mauroalderete/3dprinter/Zero/Design Model 0/CuplaFlexible58.SLDPRT

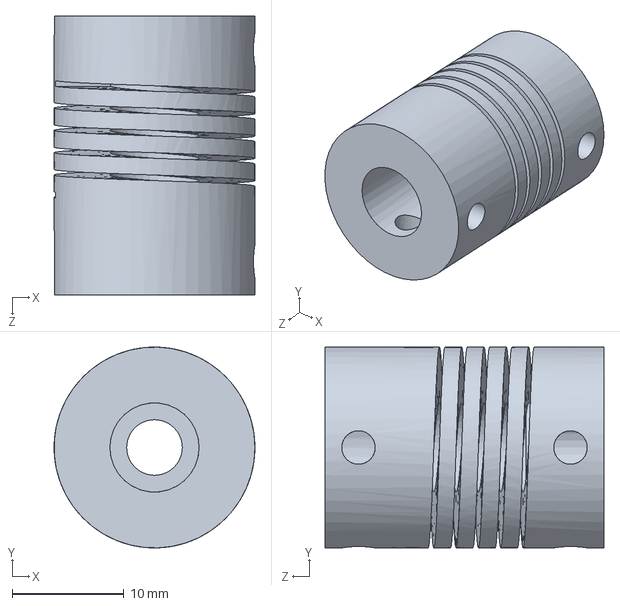
[picture p16: CAD file, 2018-10-06]
Zero/Design Model 0/CuplaFlexible58.SLDPRT
18.0 x 18.0 x 25.0 mm
