mauroalderete/3dprinter/Zero/Design Model 0/Manufacture/LateralRight.SLDPRT

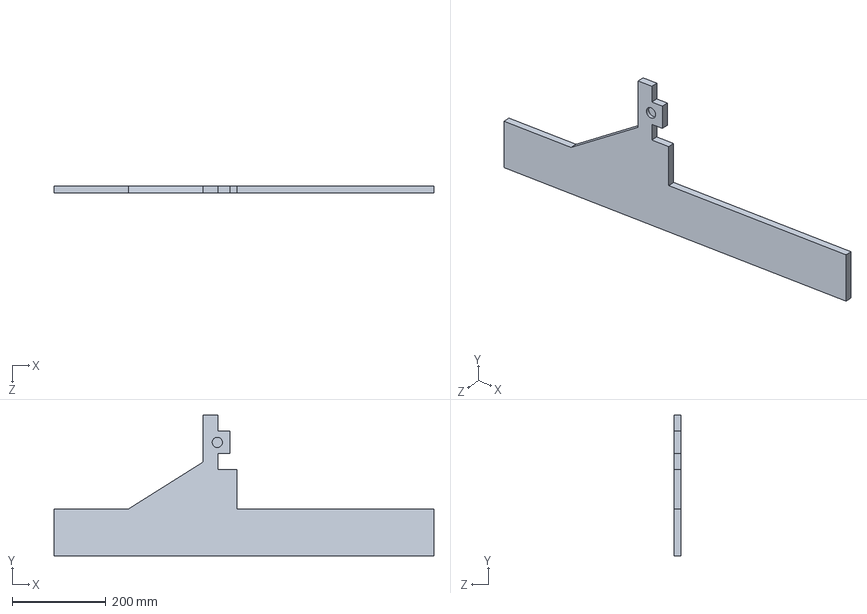
[picture p17: CAD file, 2018-10-08]
Zero/Design Model 0/Manufacture/LateralRight.SLDPRT
811.2 x 300.0 x 15.0 mm
