mauroalderete/3dprinter/Zero/Design Model 1/FuentePC.SLDPRT

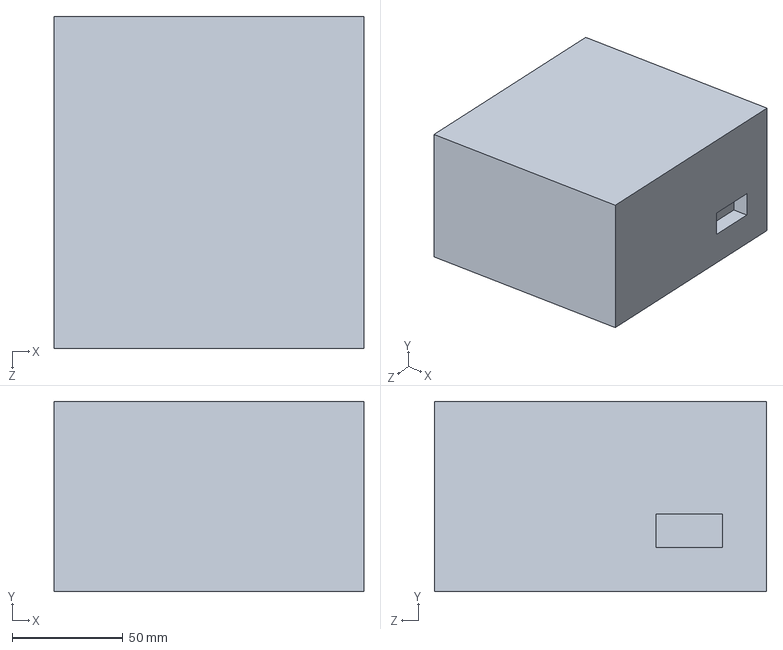
[picture p18: CAD file, 2018-10-14]
Zero/Design Model 1/FuentePC.SLDPRT
140.0 x 86.0 x 150.0 mm
