mauroalderete/3dprinter/Zero/Design Model 0/ConceptTests/EjeZ Invertido/SoporteEjeZ.SLDPRT

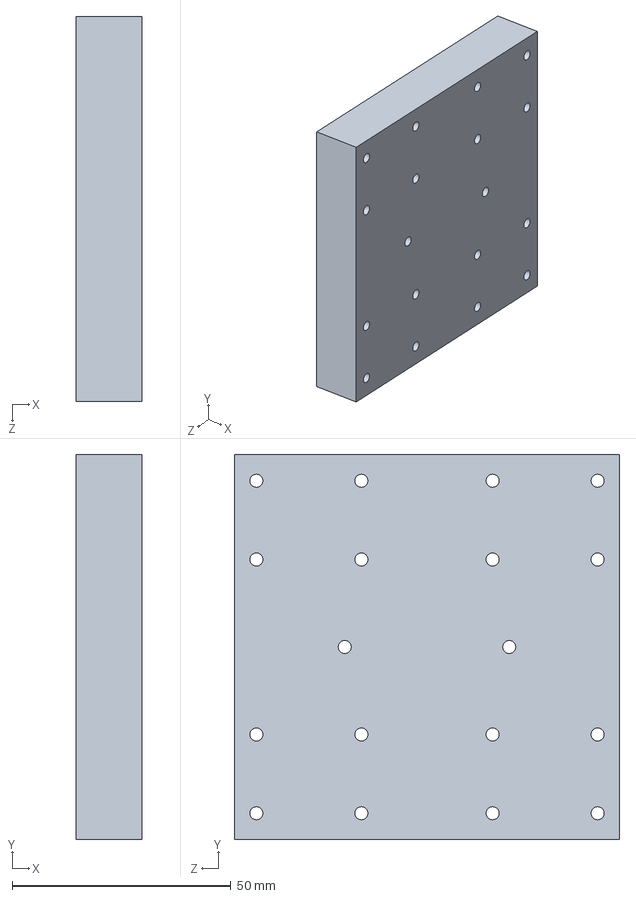
[picture p19: CAD file, 2018-10-09]
Zero/Design Model 0/ConceptTests/EjeZ Invertido/SoporteEjeZ.SLDPRT
15.0 x 88.0 x 88.0 mm
