mauroalderete/3dprinter/Zero/Design Model 0/TuercaTHSL8-Soporte.SLDPRT

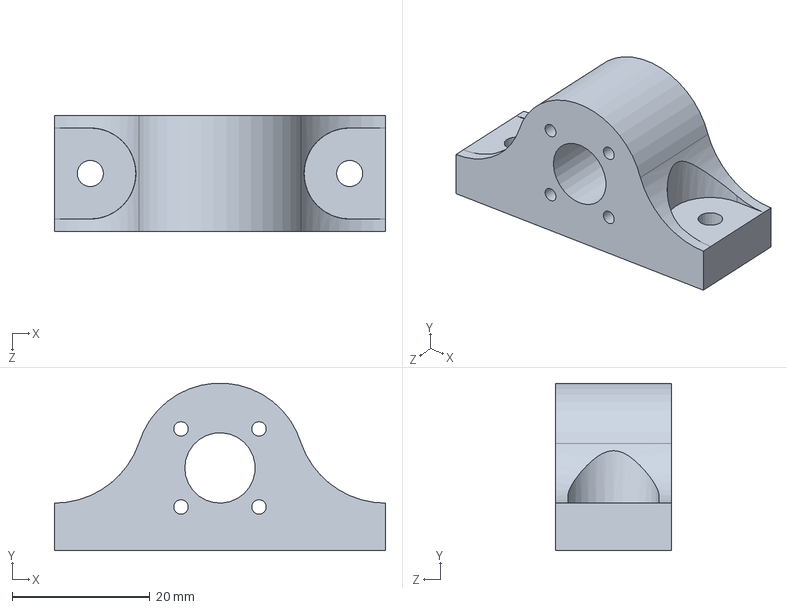
[picture p20: CAD file, 2018-10-06]
Zero/Design Model 0/TuercaTHSL8-Soporte.SLDPRT
48.0 x 24.3 x 16.8 mm
