mauroalderete/3dprinter/Zero/Design Model 1/Dremel-SoporteCabezal.SLDPRT

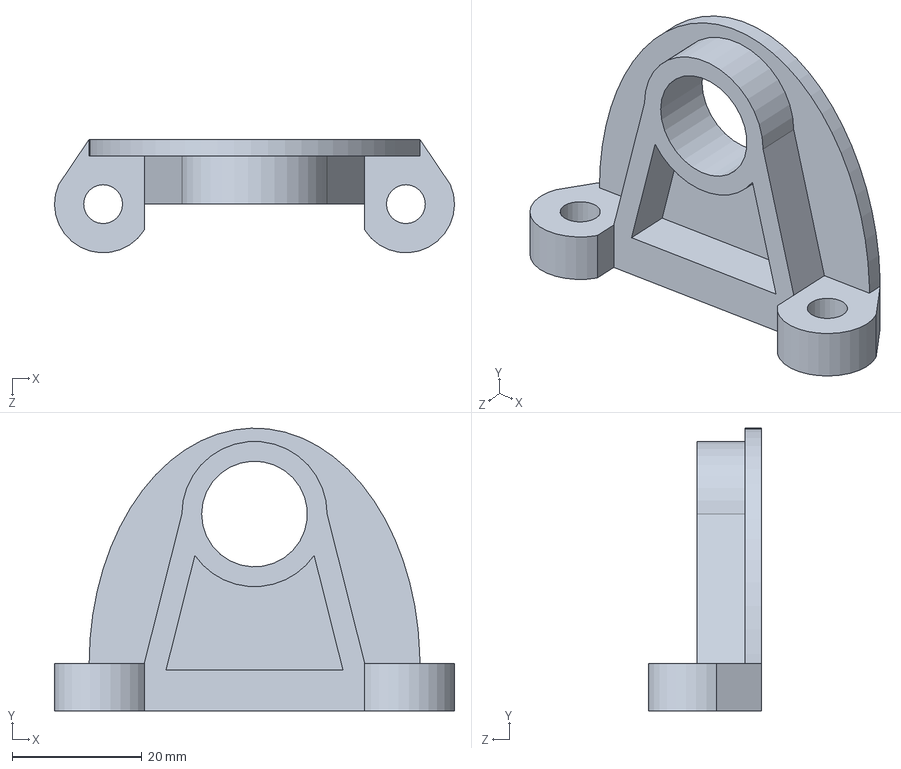
[picture p21: CAD file, 2018-10-14]
Zero/Design Model 1/Dremel-SoporteCabezal.SLDPRT
61.7 x 43.6 x 17.5 mm
