mauroalderete/3dprinter/Zero/Design Model 1/Manufacture/BaseMinitorno.SLDPRT

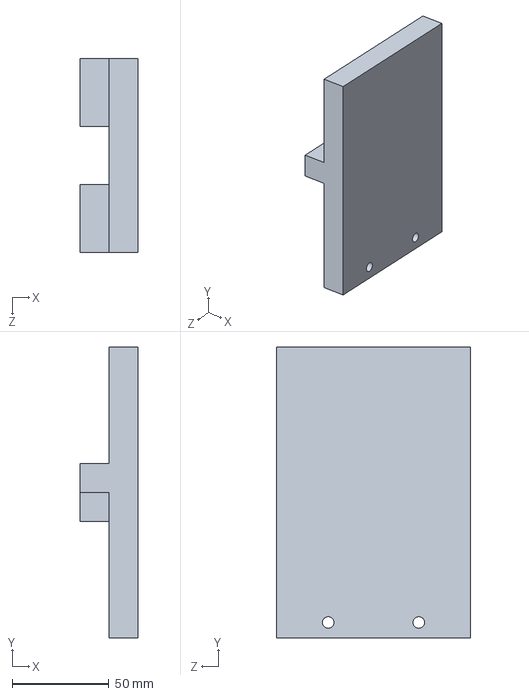
[picture p22: CAD file, 2018-10-14]
Zero/Design Model 1/Manufacture/BaseMinitorno.SLDPRT
30.0 x 150.0 x 100.0 mm
