mauroalderete/3dprinter/Zero/Design Model 0/TuercaTHSL8.SLDPRT

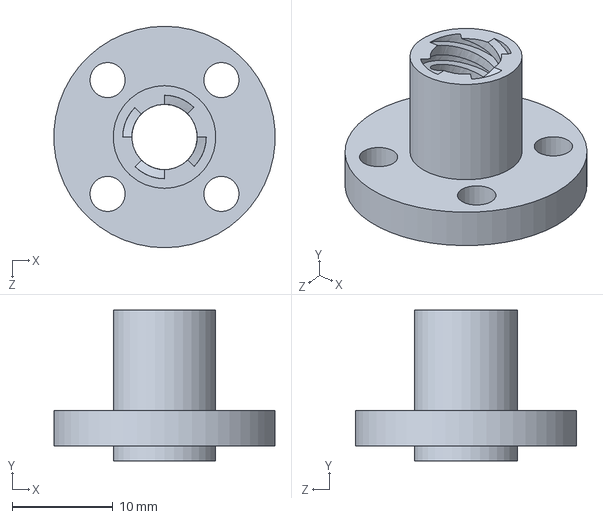
[picture p23: CAD file, 2018-10-06]
Zero/Design Model 0/TuercaTHSL8.SLDPRT
22.0 x 15.0 x 22.0 mm
