mauroalderete/3dprinter/Zero/Design Model 1/BaseElectronica.SLDPRT

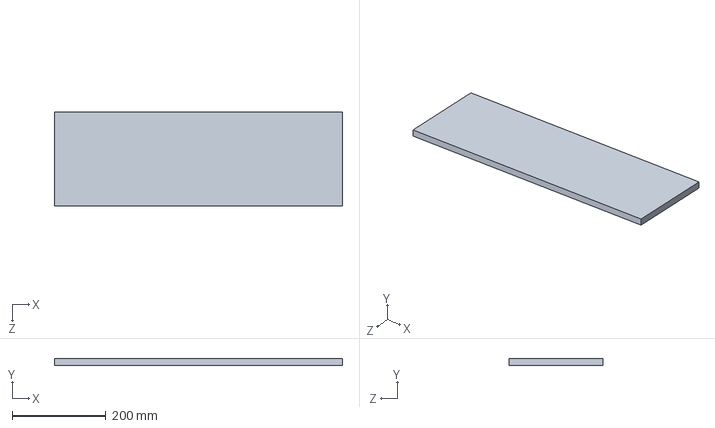
[picture p24: CAD file, 2018-10-14]
Zero/Design Model 1/BaseElectronica.SLDPRT
615.0 x 15.0 x 200.0 mm
