mauroalderete/3dprinter/Zero/Design Model 1/Manufacture/ZFloor.SLDPRT

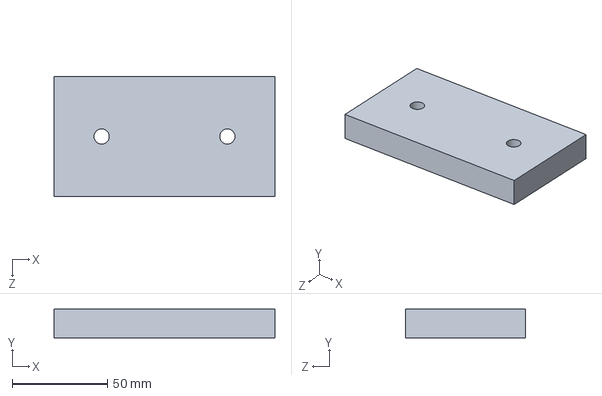
[picture p25: CAD file, 2018-10-12]
Zero/Design Model 1/Manufacture/ZFloor.SLDPRT
116.0 x 15.0 x 63.0 mm
