mauroalderete/3dprinter/Zero/Design Model 0/Manufacture/LateralArco.SLDPRT

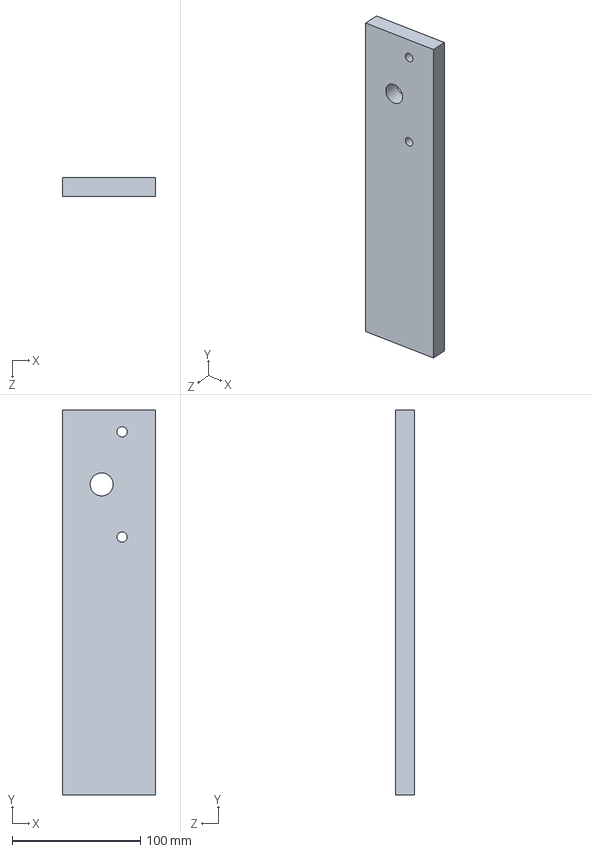
[picture p26: CAD file, 2018-10-08]
Zero/Design Model 0/Manufacture/LateralArco.SLDPRT
72.5 x 300.0 x 15.0 mm
