mauroalderete/3dprinter/Zero/Design Model 1/Manufacture/BaseTool.SLDPRT

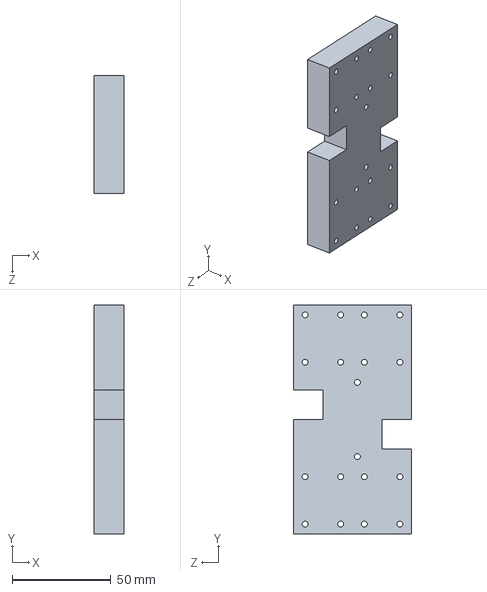
[picture p27: CAD file, 2018-10-12]
Zero/Design Model 1/Manufacture/BaseTool.SLDPRT
15.0 x 116.0 x 60.0 mm
