mauroalderete/3dprinter/Zero/Design Model 1/Minitorno.SLDPRT

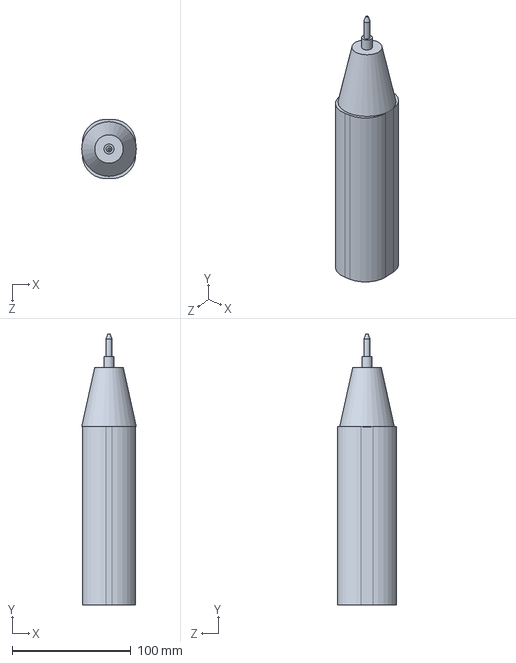
[picture p28: CAD file, 2018-10-14]
Zero/Design Model 1/Minitorno.SLDPRT
46.0 x 228.0 x 50.0 mm
