mauroalderete/3dprinter/Zero/Design Model 0/Manufacture/LateralSoporteEjeX.SLDPRT

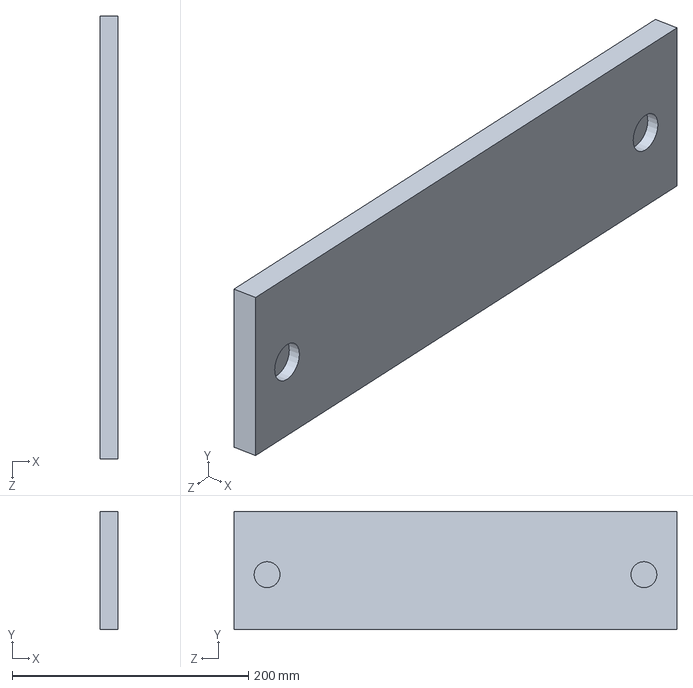
[picture p29: CAD file, 2018-10-08]
Zero/Design Model 0/Manufacture/LateralSoporteEjeX.SLDPRT
15.0 x 100.0 x 375.0 mm
