mauroalderete/3dprinter/Zero/Design Model 0/NEMA17-Soporte.SLDPRT

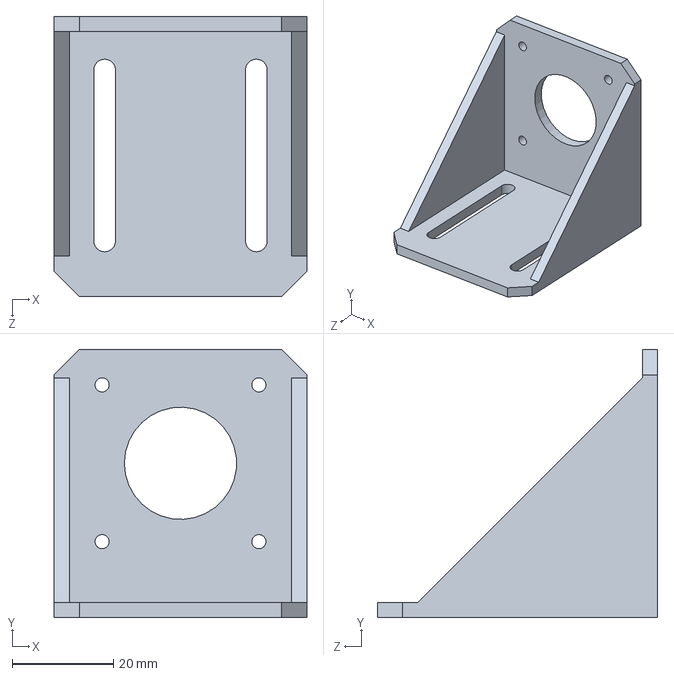
[picture p30: CAD file, 2018-10-06]
Zero/Design Model 0/NEMA17-Soporte.SLDPRT
50.0 x 53.0 x 55.4 mm
