mauroalderete/3dprinter/Zero/Design Model 1/Manufacture/BaseExtrusor.SLDPRT

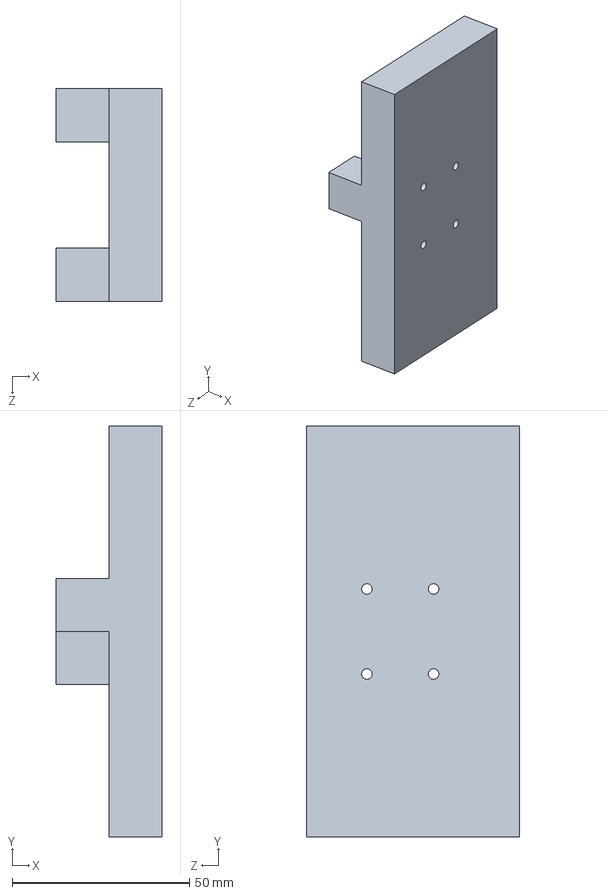
[picture p31: CAD file, 2018-10-12]
Zero/Design Model 1/Manufacture/BaseExtrusor.SLDPRT
30.0 x 116.0 x 60.0 mm
