mauroalderete/3dprinter/Zero/Design Model 1/ZPiso.SLDPRT

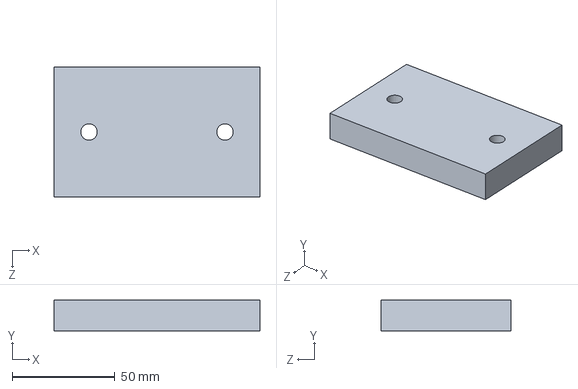
[picture p32: CAD file, 2018-10-12]
Zero/Design Model 1/ZPiso.SLDPRT
100.0 x 15.0 x 63.0 mm
