mauroalderete/3dprinter/Zero/Design Model 1/Manufacture/ZMotorBoxLeftA.SLDPRT

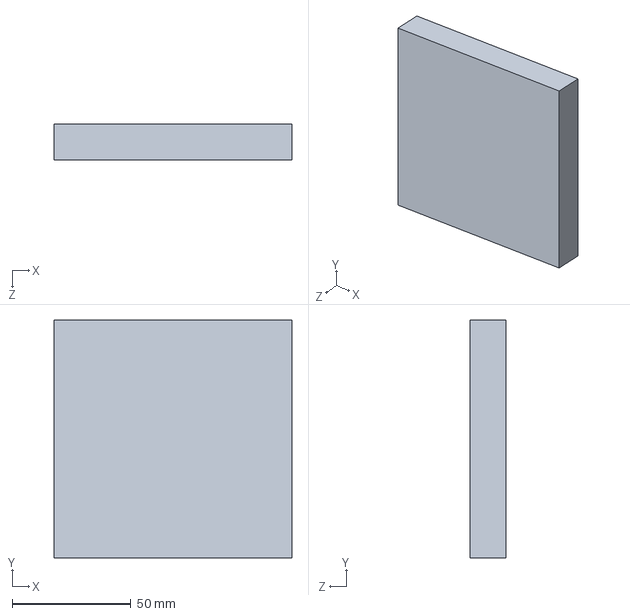
[picture p33: CAD file, 2018-10-12]
Zero/Design Model 1/Manufacture/ZMotorBoxLeftA.SLDPRT
100.0 x 100.0 x 15.0 mm
