mauroalderete/3dprinter/Zero/Design Model 1/ZArco.SLDPRT

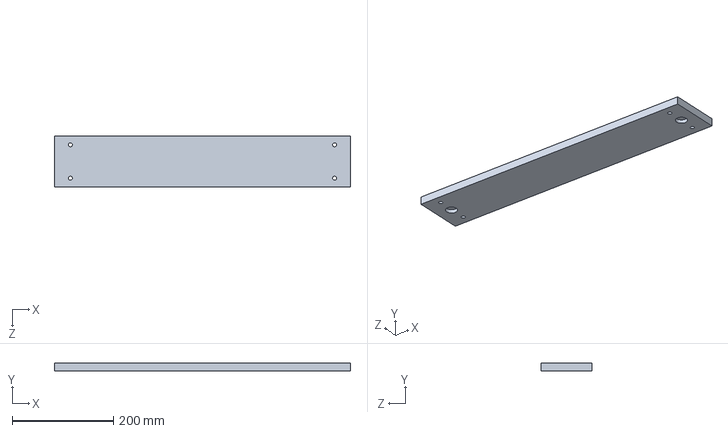
[picture p34: CAD file, 2018-10-12]
Zero/Design Model 1/ZArco.SLDPRT
585.0 x 15.0 x 100.0 mm
