mauroalderete/3dprinter/Zero/Design Model 0/ArduinoMEGA-Simple.SLDPRT

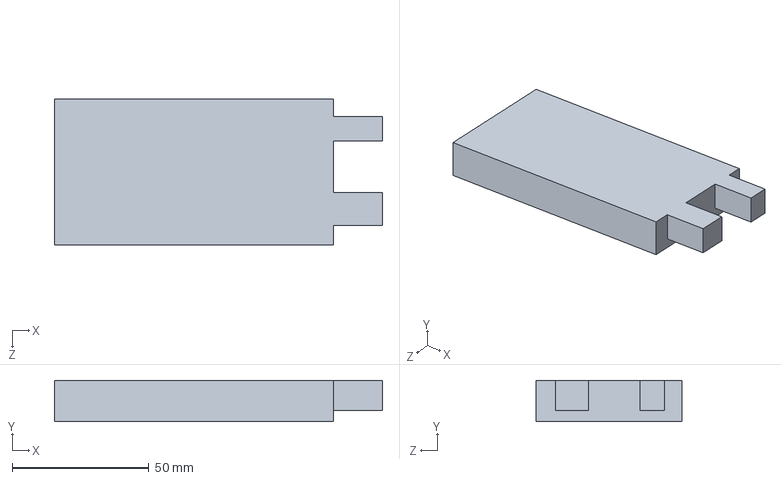
[picture p35: CAD file, 2018-10-05]
Zero/Design Model 0/ArduinoMEGA-Simple.SLDPRT
120.0 x 15.0 x 53.5 mm
