mauroalderete/3dprinter/Zero/Design Model 1/Extrusor MK9-Simple.SLDPRT

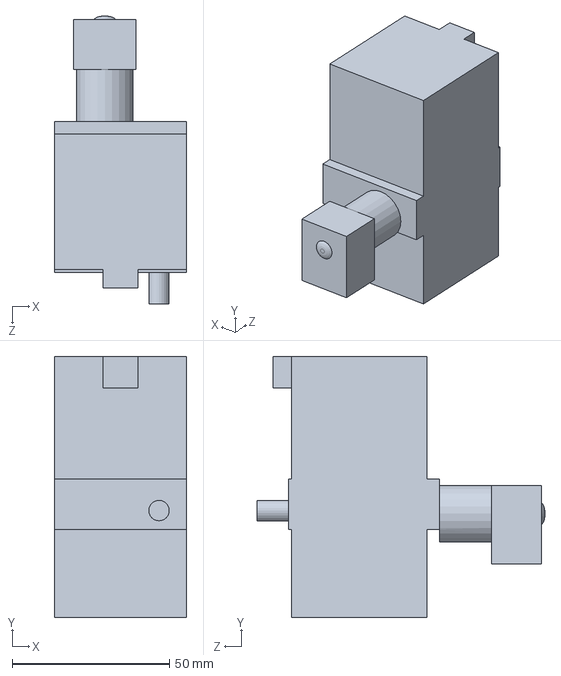
[picture p37: CAD file, 2018-10-12]
Zero/Design Model 1/Extrusor MK9-Simple.SLDPRT
42.0 x 83.0 x 91.5 mm
