mauroalderete/3dprinter/Zero/Design Model 1/Manufacture/Base.SLDPRT

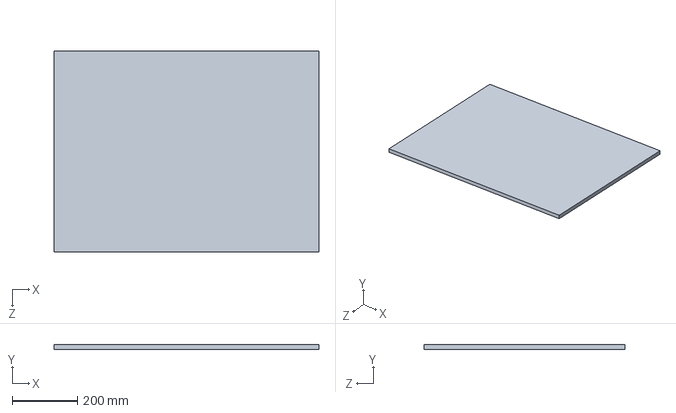
[picture p38: CAD file, 2018-10-12]
Zero/Design Model 1/Manufacture/Base.SLDPRT
811.2 x 15.0 x 615.0 mm
