mauroalderete/3dprinter/Zero/Design Model 0/RAMP14-Simple.SLDPRT

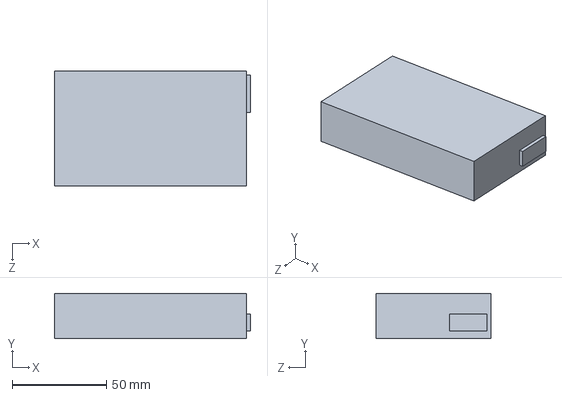
[picture p39: CAD file, 2018-10-05]
Zero/Design Model 0/RAMP14-Simple.SLDPRT
104.0 x 24.0 x 61.0 mm
