mauroalderete/3dprinter/Zero/Design Model 1/Manufacture/ZSoporteCarroRight.SLDPRT

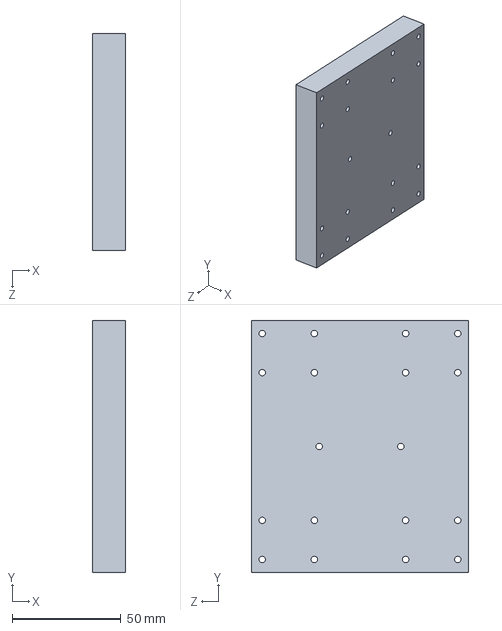
[picture p40: CAD file, 2018-10-12]
Zero/Design Model 1/Manufacture/ZSoporteCarroRight.SLDPRT
15.0 x 116.0 x 100.0 mm
