mauroalderete/3dprinter/Zero/Design Model 0/Manufacture/WorkArea.SLDPRT

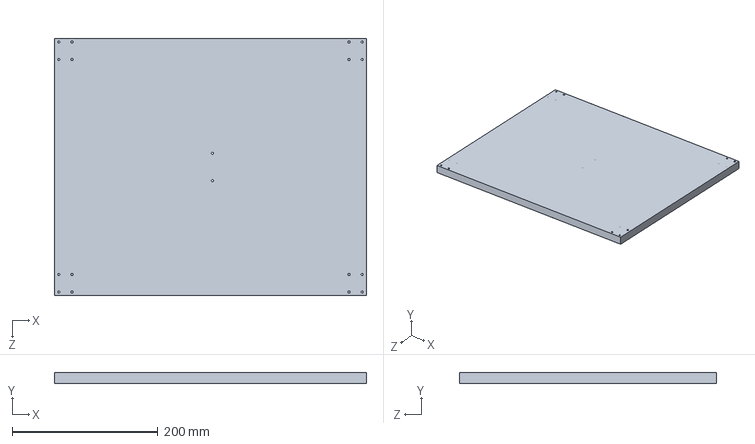
[picture p41: CAD file, 2018-10-07]
Zero/Design Model 0/Manufacture/WorkArea.SLDPRT
428.0 x 15.0 x 353.0 mm
