mauroalderete/3dprinter/Zero/Design Model 0/TornilloTHSL8x40.SLDPRT

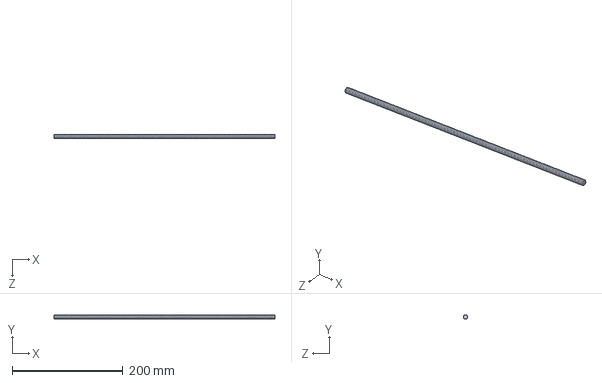
[picture p42: CAD file, 2018-10-05]
Zero/Design Model 0/TornilloTHSL8x40.SLDPRT
400.0 x 8.00 x 8.00 mm
