mauroalderete/3dprinter/Zero/Design Model 0/Manufacture/Base.SLDPRT

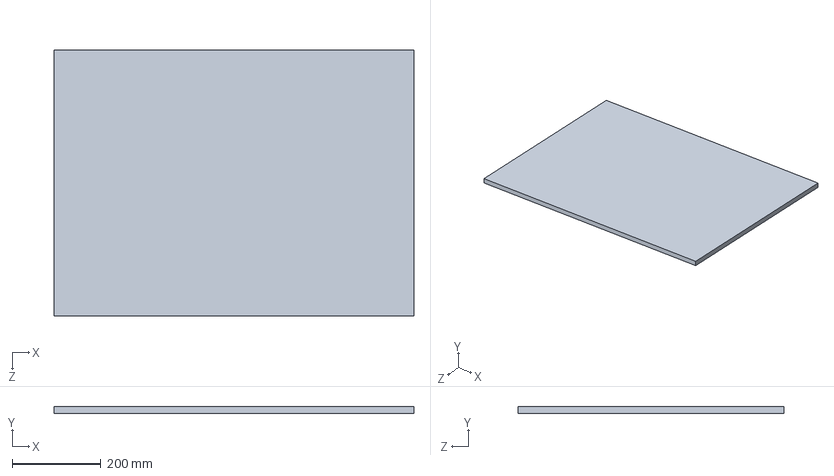
[picture p43: CAD file, 2018-10-07]
Zero/Design Model 0/Manufacture/Base.SLDPRT
811.2 x 15.0 x 600.0 mm
