mauroalderete/3dprinter/Zero/Design Model 0/TornilloTHSL8x40-ExtraSimple.SLDPRT

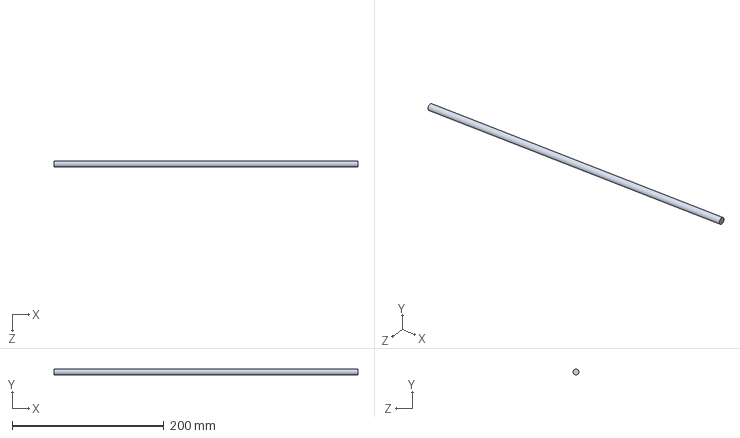
[picture p44: CAD file, 2018-10-05]
Zero/Design Model 0/TornilloTHSL8x40-ExtraSimple.SLDPRT
400.0 x 8.00 x 8.00 mm
