mauroalderete/3dprinter/Zero/Design Model 1/Manufacture/SoporteCupla.SLDPRT

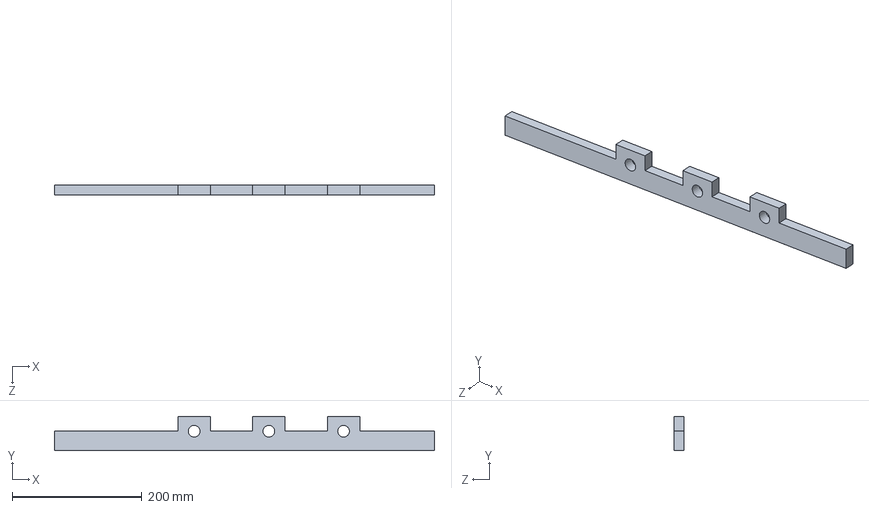
[picture p45: CAD file, 2018-10-12]
Zero/Design Model 1/Manufacture/SoporteCupla.SLDPRT
585.0 x 53.0 x 15.0 mm
