mauroalderete/3dprinter/Zero/Design Model 0/Dremel-SoporteCuerpo.SLDPRT

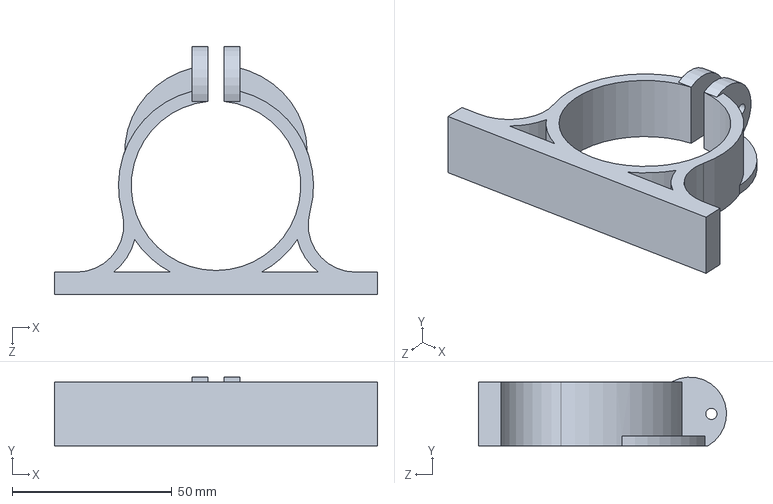
[picture p46: CAD file, 2018-10-05]
Zero/Design Model 0/Dremel-SoporteCuerpo.SLDPRT
101.0 x 21.5 x 77.5 mm
