mauroalderete/3dprinter/Zero/Design Model 0/Manufacture/VarillaAcero8-X.SLDPRT

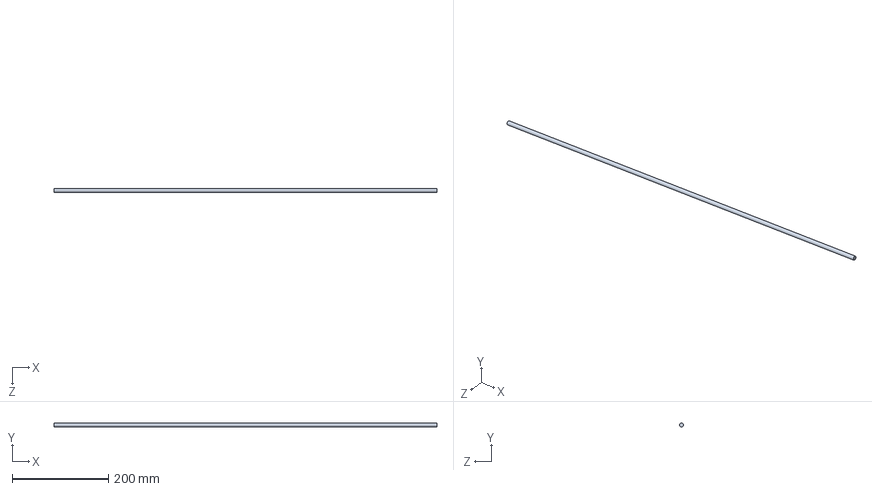
[picture p47: CAD file, 2018-10-07]
Zero/Design Model 0/Manufacture/VarillaAcero8-X.SLDPRT
795.2 x 8.00 x 8.00 mm
