mauroalderete/3dprinter/Zero/Design Model 1/Manufacture/VarillaAcero8-Y.SLDPRT

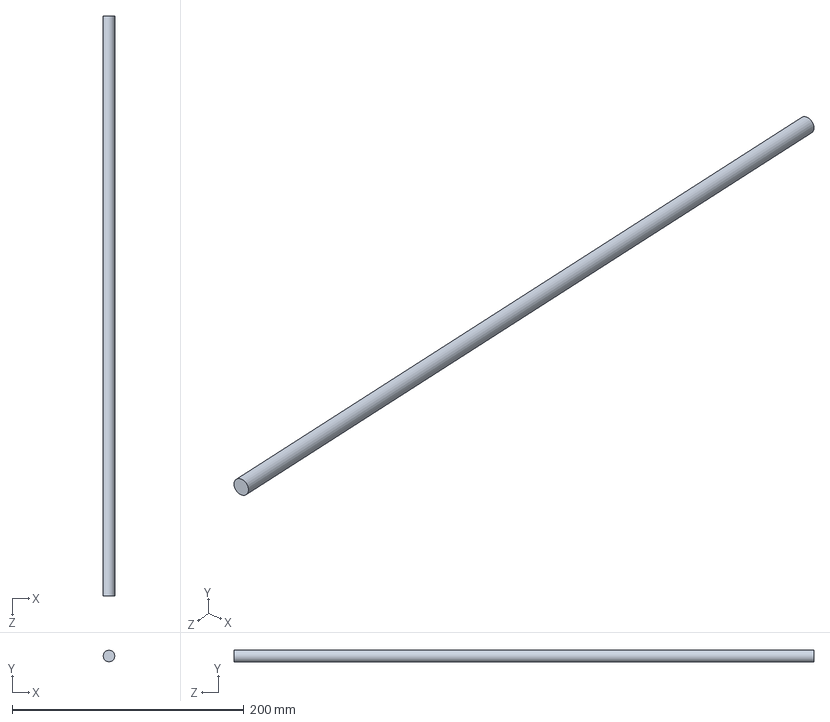
[picture p48: CAD file, 2018-10-12]
Zero/Design Model 1/Manufacture/VarillaAcero8-Y.SLDPRT
10.0 x 10.0 x 500.0 mm
