mauroalderete/3dprinter/Zero/Design Model 0/Manufacture/TacoEjeY.SLDPRT

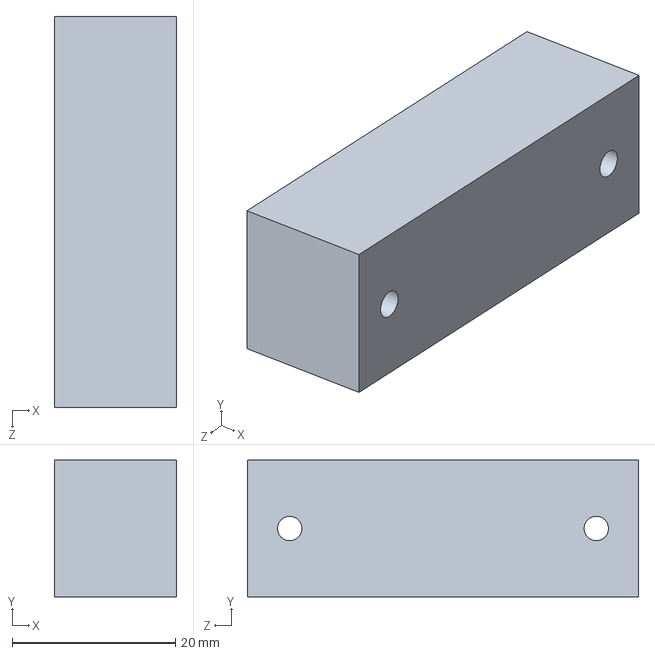
[picture p49: CAD file, 2018-10-07]
Zero/Design Model 0/Manufacture/TacoEjeY.SLDPRT
15.0 x 16.8 x 48.0 mm
