mauroalderete/3dprinter/Zero/Design Model 0/Manufacture/SoporteTHSLEjeX.SLDPRT

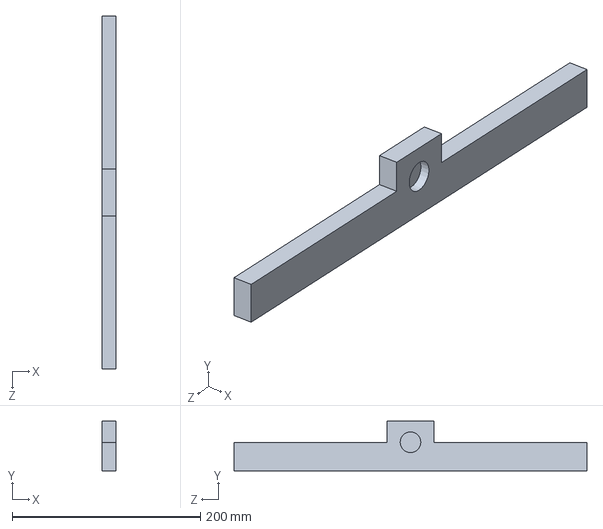
[picture p51: CAD file, 2018-10-07]
Zero/Design Model 0/Manufacture/SoporteTHSLEjeX.SLDPRT
15.0 x 53.0 x 375.0 mm
