mauroalderete/3dprinter/Zero/Design Model 1/Manufacture/XDescansoEjes.SLDPRT

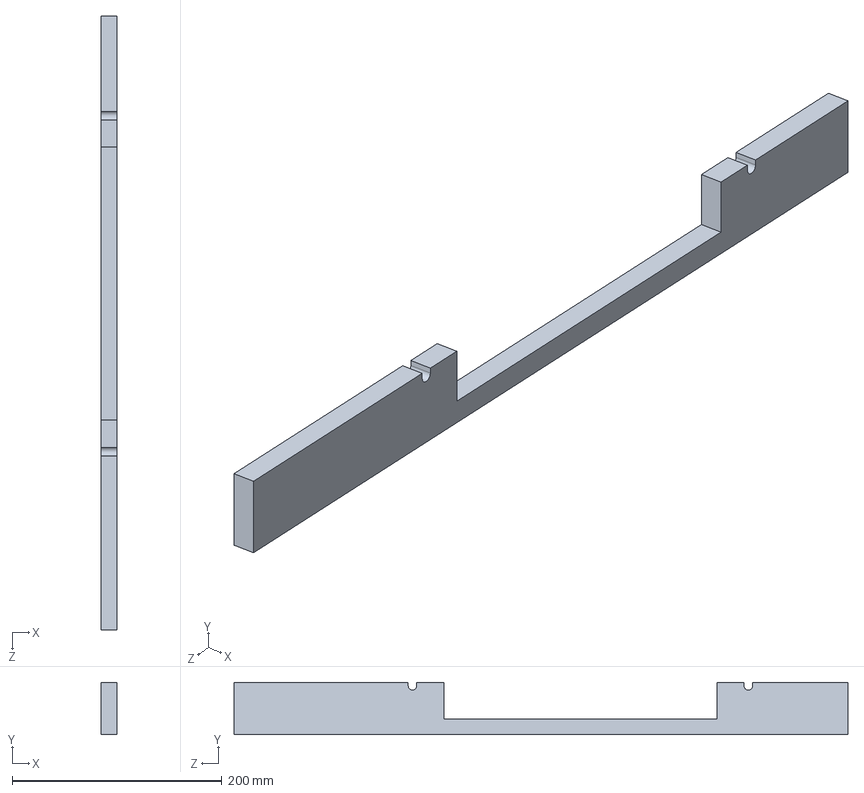
[picture p52: CAD file, 2018-10-12]
Zero/Design Model 1/Manufacture/XDescansoEjes.SLDPRT
15.0 x 50.0 x 585.0 mm
