mauroalderete/3dprinter/Zero/Design Model 0/Extrusor MK8-SoportePrusa.SLDPRT

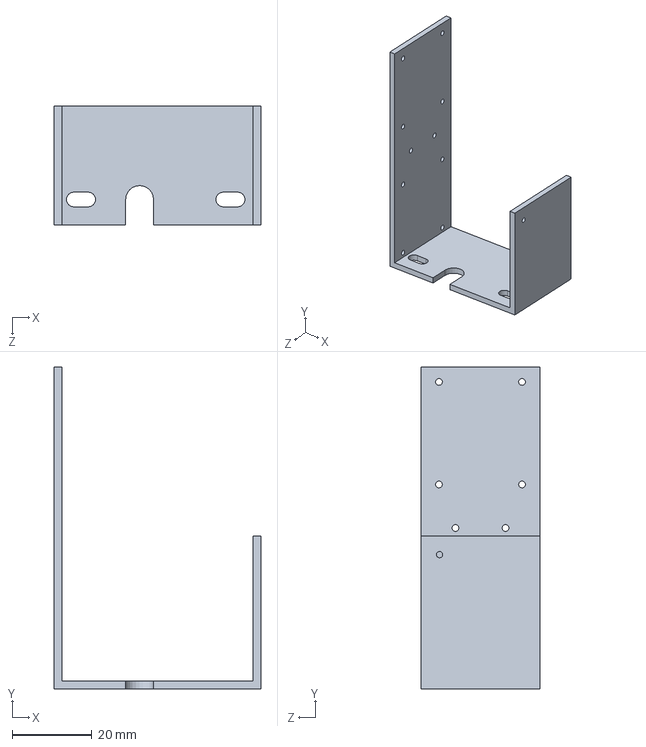
[picture p53: CAD file, 2018-10-05]
Zero/Design Model 0/Extrusor MK8-SoportePrusa.SLDPRT
52.0 x 81.0 x 30.0 mm
