mauroalderete/3dprinter/Zero/Design Model 0/Manufacture/LateralLarge.SLDPRT

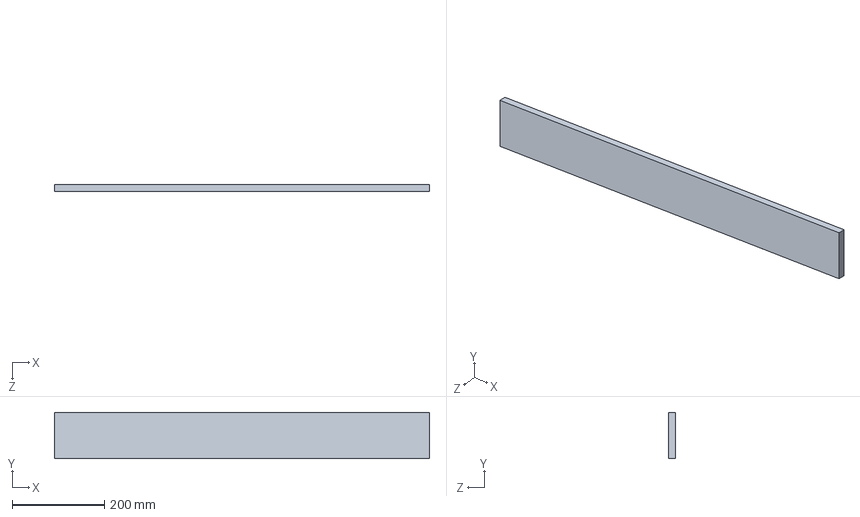
[picture p54: CAD file, 2018-10-07]
Zero/Design Model 0/Manufacture/LateralLarge.SLDPRT
811.2 x 100.0 x 15.0 mm
