mauroalderete/3dprinter/Zero/Design Model 0/Rodamiento Lineal LM8UU.SLDPRT

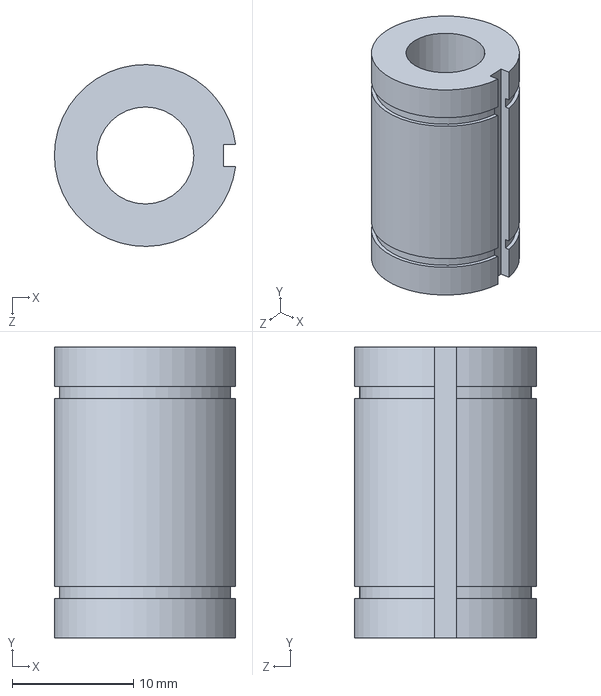
[picture p55: CAD file, 2018-10-04]
Zero/Design Model 0/Rodamiento Lineal LM8UU.SLDPRT
14.9 x 24.0 x 15.0 mm
