mauroalderete/3dprinter/Zero/Design Model 1/Manufacture/VarillaAcero8-Z.SLDPRT

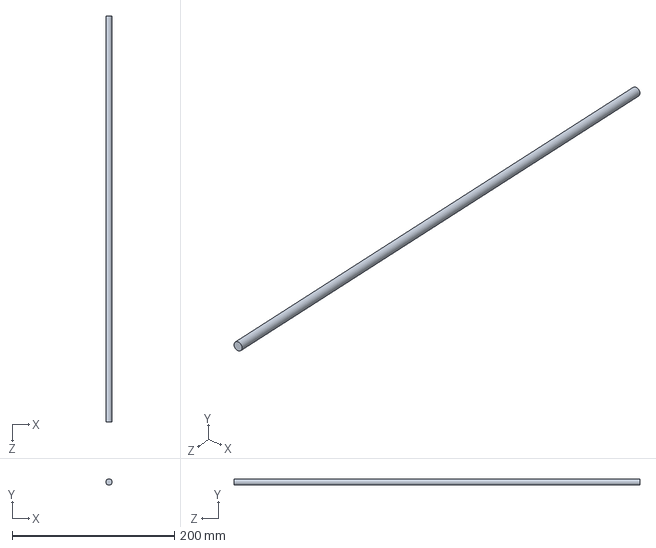
[picture p56: CAD file, 2018-10-12]
Zero/Design Model 1/Manufacture/VarillaAcero8-Z.SLDPRT
8.00 x 8.00 x 500.0 mm
