mauroalderete/3dprinter/Zero/Design Model 0/Manufacture/VarillaAcero8-Y.SLDPRT

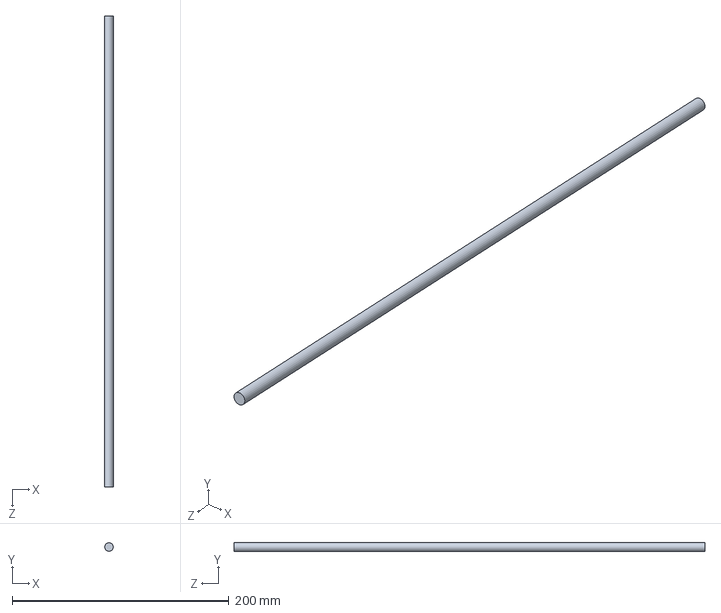
[picture p57: CAD file, 2018-10-07]
Zero/Design Model 0/Manufacture/VarillaAcero8-Y.SLDPRT
8.00 x 8.00 x 435.0 mm
