mauroalderete/3dprinter/Zero/Design Model 0/Rodamiento Lineal LM8UU-Soporte.SLDPRT

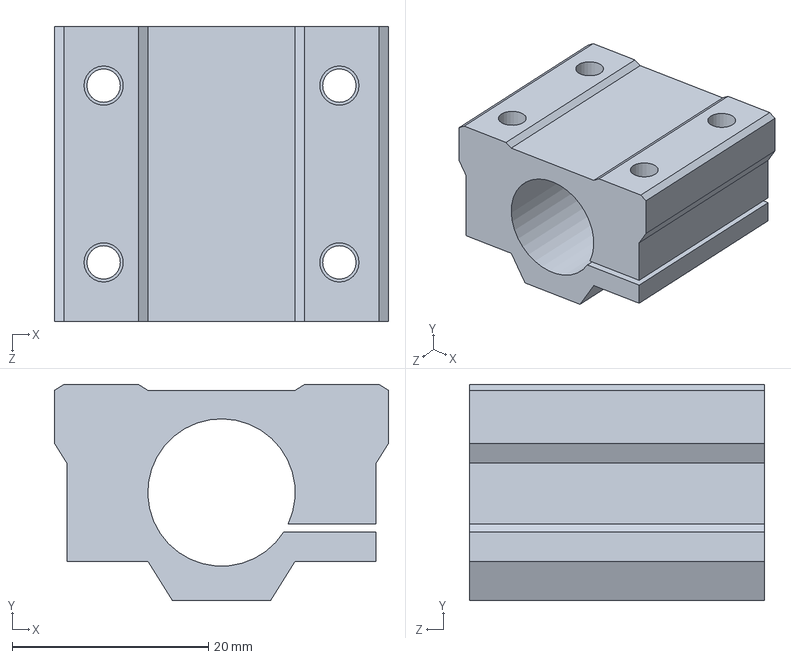
[picture p58: CAD file, 2018-10-04]
Zero/Design Model 0/Rodamiento Lineal LM8UU-Soporte.SLDPRT
34.0 x 22.0 x 30.0 mm
