mauroalderete/3dprinter/Zero/Design Model 0/Manufacture/ColumnaEjesX.SLDPRT

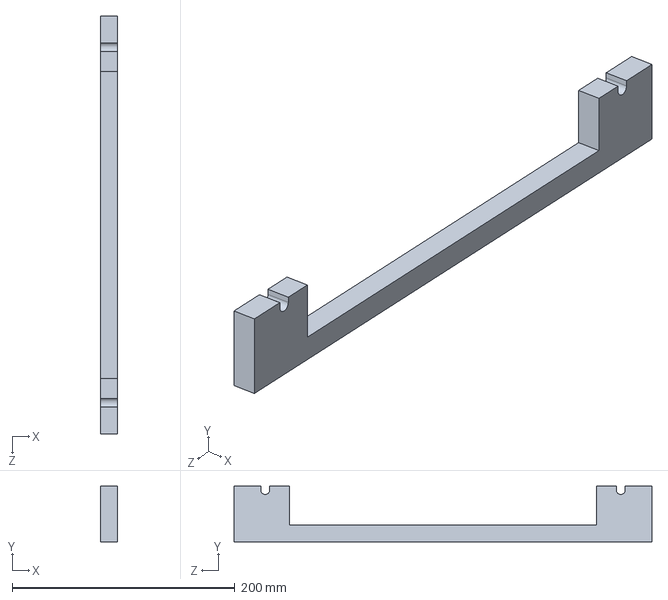
[picture p59: CAD file, 2018-10-07]
Zero/Design Model 0/Manufacture/ColumnaEjesX.SLDPRT
15.0 x 50.0 x 375.0 mm
