mauroalderete/3dprinter/Zero/Design Model 0/NEMA17.SLDPRT

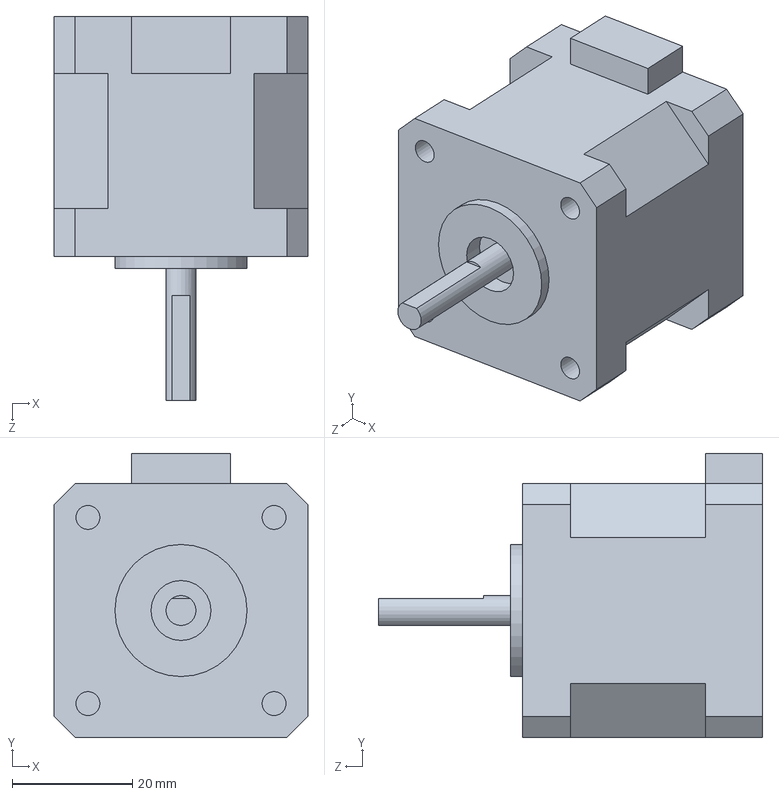
[picture p60: CAD file, 2018-10-04]
Zero/Design Model 0/NEMA17.SLDPRT
42.3 x 47.3 x 64.0 mm
