mauroalderete/3dprinter/Zero/Design Model 0/Extrusor MK8-SoporteA.SLDPRT

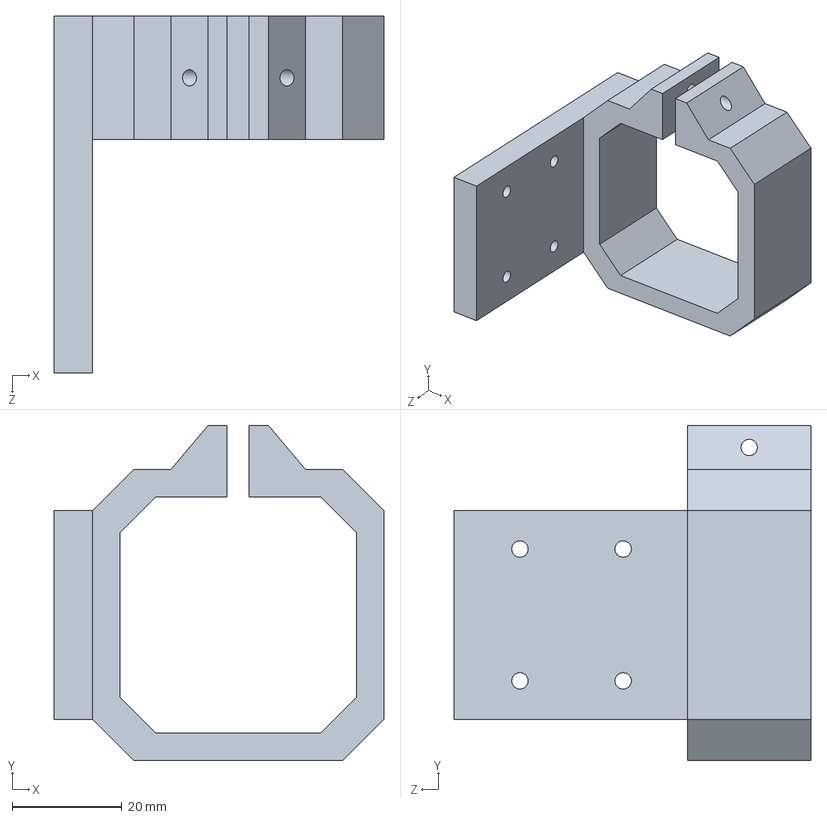
[picture p61: CAD file, 2018-10-04]
Zero/Design Model 0/Extrusor MK8-SoporteA.SLDPRT
60.0 x 61.0 x 65.0 mm
