mauroalderete/3dprinter/Zero/Design Model 0/Manufacture/Taco.SLDPRT

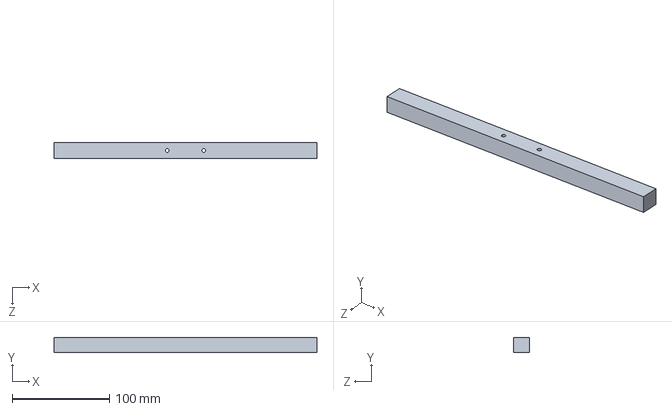
[picture p62: CAD file, 2018-10-07]
Zero/Design Model 0/Manufacture/Taco.SLDPRT
270.0 x 15.0 x 16.8 mm
