mauroalderete/3dprinter/Zero/Design Model 1/Manufacture/XCarro.SLDPRT

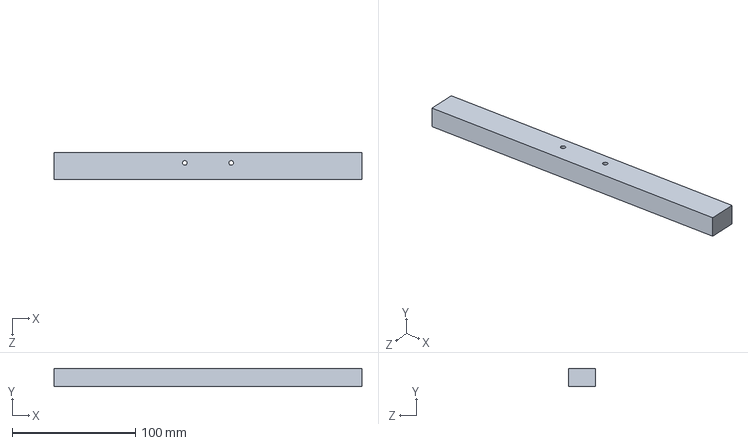
[picture p63: CAD file, 2018-10-12]
Zero/Design Model 1/Manufacture/XCarro.SLDPRT
250.0 x 15.0 x 22.0 mm
