mauroalderete/3dprinter/Zero/Design Model 1/Manufacture/WorkArea.SLDPRT

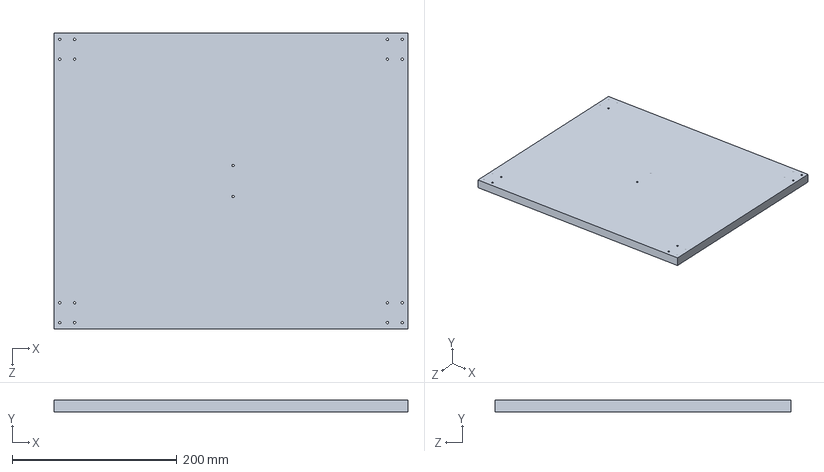
[picture p64: CAD file, 2018-10-12]
Zero/Design Model 1/Manufacture/WorkArea.SLDPRT
430.0 x 15.0 x 360.0 mm
