mauroalderete/3dprinter/Zero/Design Model 1/Manufacture/Taco.SLDPRT

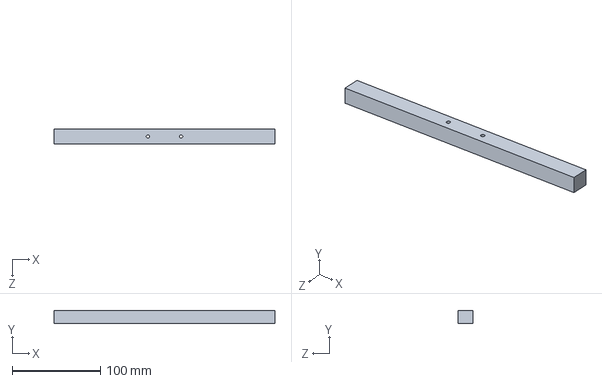
[picture p65: CAD file, 2018-10-12]
Zero/Design Model 1/Manufacture/Taco.SLDPRT
250.0 x 15.0 x 16.8 mm
