mauroalderete/3dprinter/Zero/Design Model 1/Manufacture/ZMotorBoxLeftB.SLDPRT

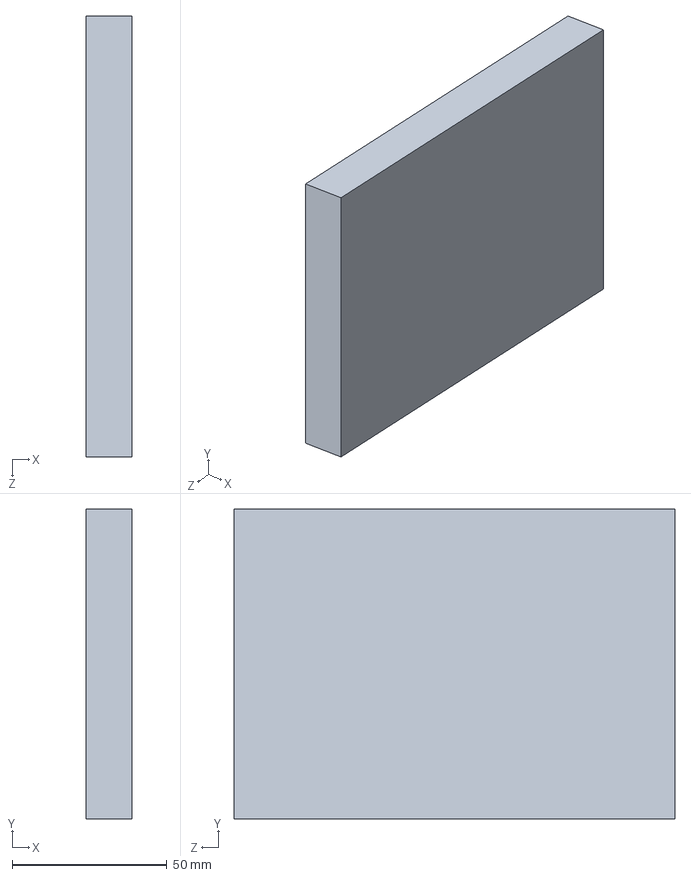
[picture p66: CAD file, 2018-10-12]
Zero/Design Model 1/Manufacture/ZMotorBoxLeftB.SLDPRT
15.0 x 100.0 x 142.4 mm
