mauroalderete/3dprinter/Zero/Design Model 1/Manufacture/YSoporteMotor.SLDPRT

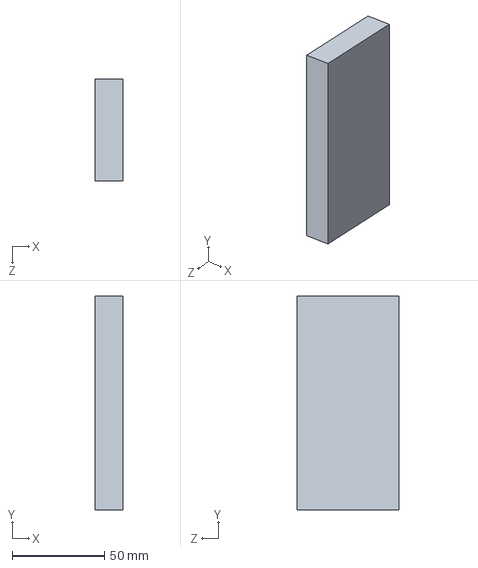
[picture p67: CAD file, 2018-10-12]
Zero/Design Model 1/Manufacture/YSoporteMotor.SLDPRT
15.0 x 116.0 x 55.4 mm
